alvaroalea/plusD-clone/docs/6196-plus-D-Clone2.jpg

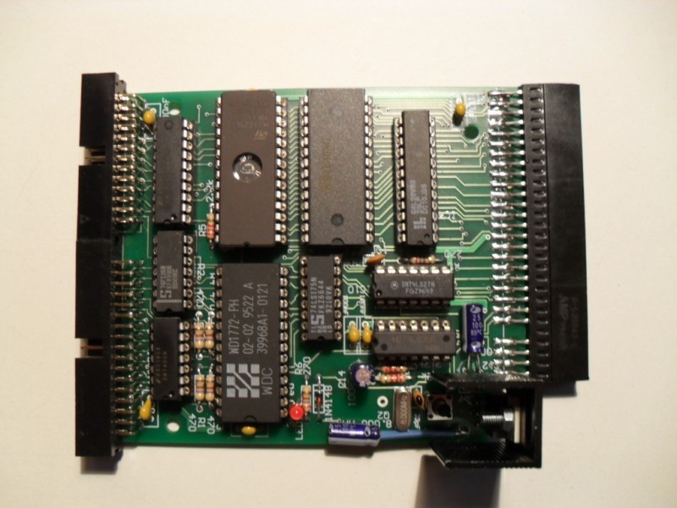
docs/6196-plus-D-Clone2.jpg
