alvaroalea/plusD-clone/docs/9922_20150616_185526_500px.jpg

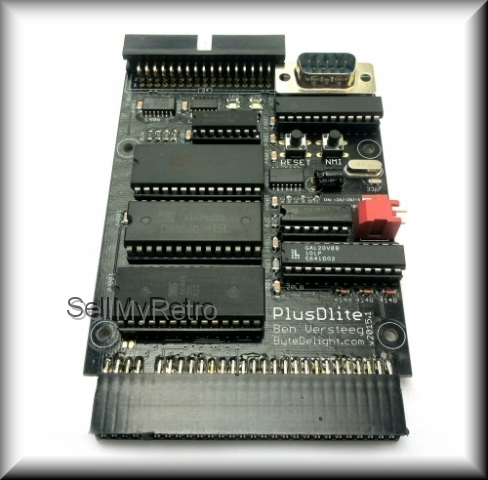
docs/9922_20150616_185526_500px.jpg
