alvaroalea/plusD-clone/docs/Disk and Interface.jpg

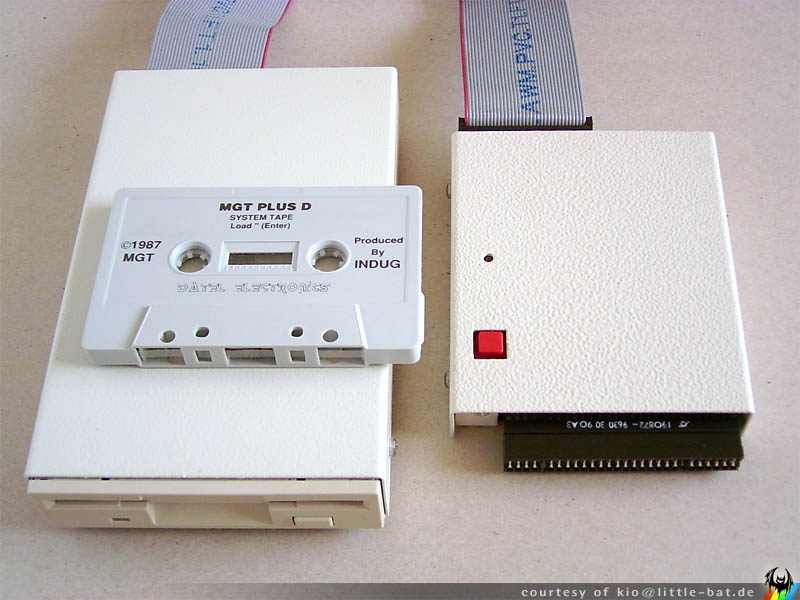
docs/Disk and Interface.jpg
