alvaroalea/plusD-clone/docs/Interface open rear.jpg

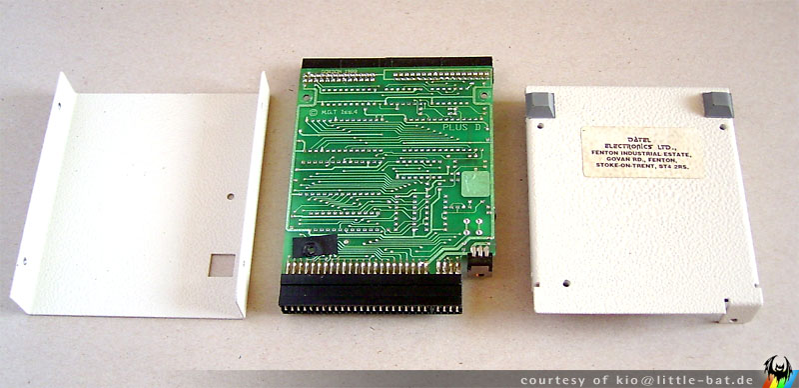
docs/Interface open rear.jpg
