alvaroalea/plusD-clone/docs/plusdelite_whcase_grey.jpg

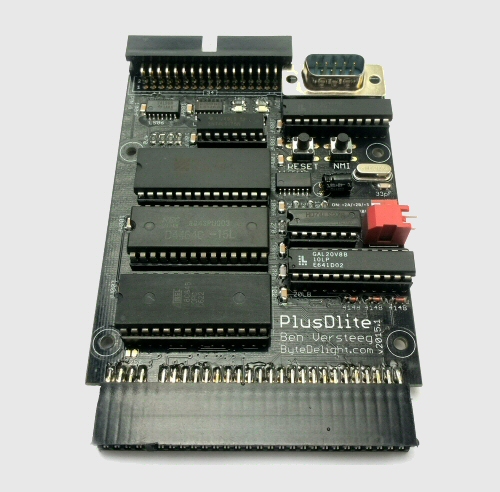
docs/plusdelite_whcase_grey.jpg
